AngelVeloz1506/TEAM-DELTA-WRO-2025-Panama/models/Prototypes/v2.jpg

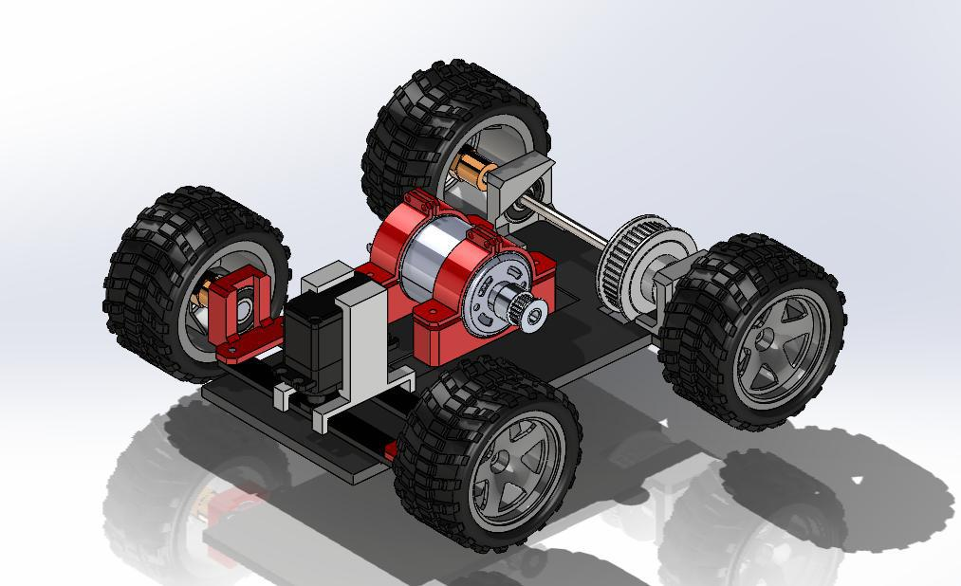
models/Prototypes/v2.jpg
