AngelVeloz1506/TEAM-DELTA-WRO-2025-Panama/models/Prototypes/v3.jpg

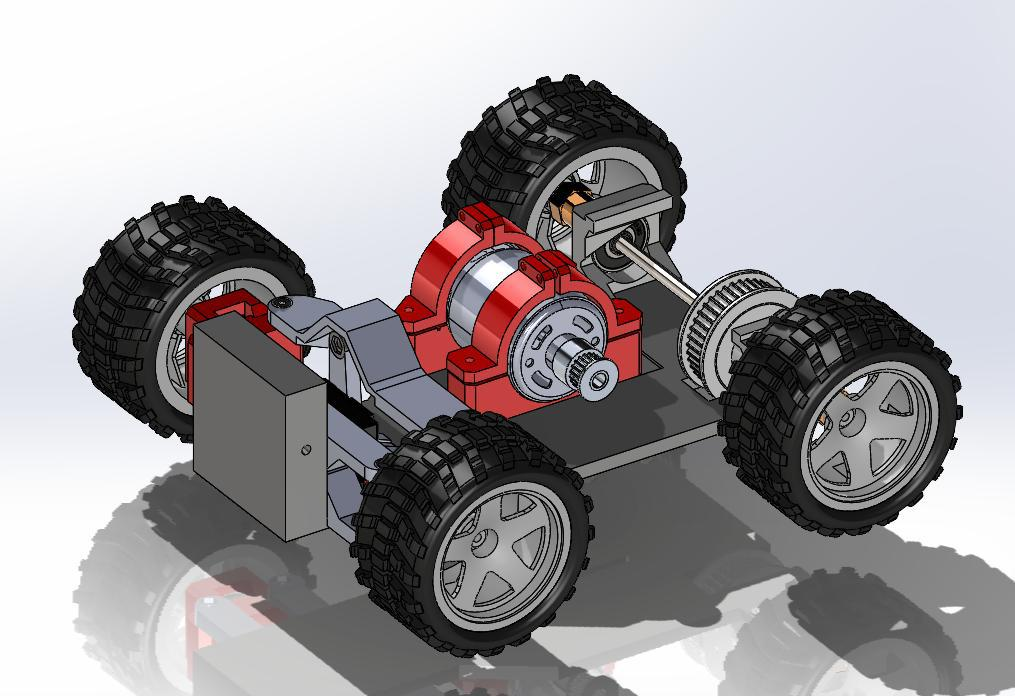
models/Prototypes/v3.jpg
