AngelVeloz1506/TEAM-DELTA-WRO-2025-Panama/v-photos/delta.jpg

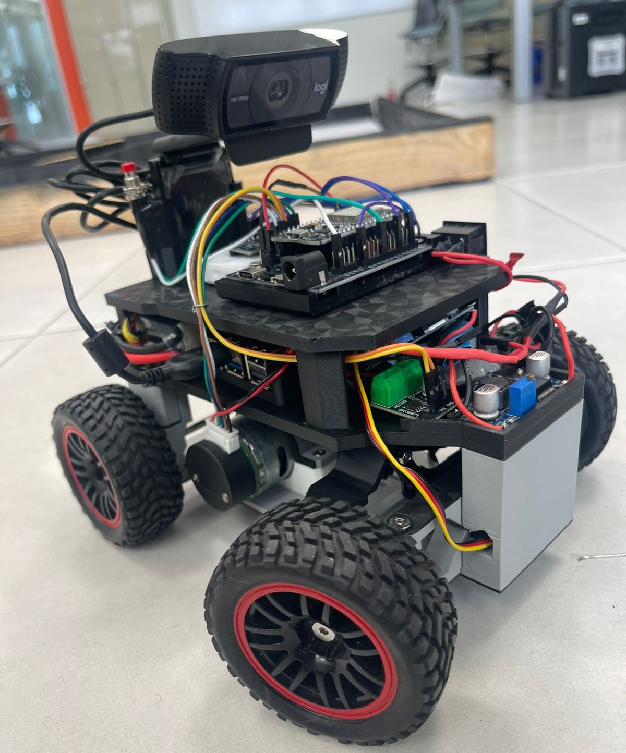
v-photos/delta.jpg
