AngelVeloz1506/TEAM-DELTA-WRO-2025-Panama/v-photos/first pic.jpg

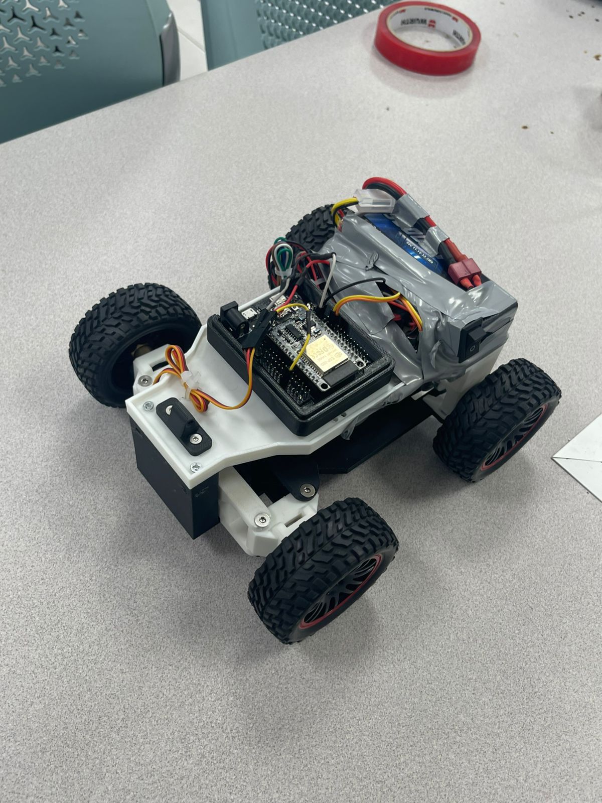
v-photos/first pic.jpg
