AngelVeloz1506/TEAM-DELTA-WRO-2025-Panama/models/Prototypes/V6.5/STL/Separador.SLDPRT

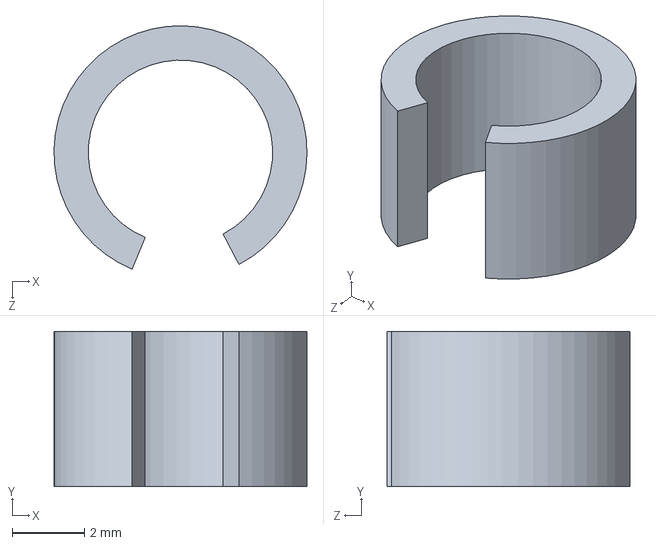
[picture p47: CAD file, 2025-08-24]
models/Prototypes/V6.5/STL/Separador.SLDPRT
7.00 x 4.30 x 6.73 mm
