AngelVeloz1506/TEAM-DELTA-WRO-2025-Panama/models/Prototypes/V6.5/Ultrasonic sensor.SLDPRT

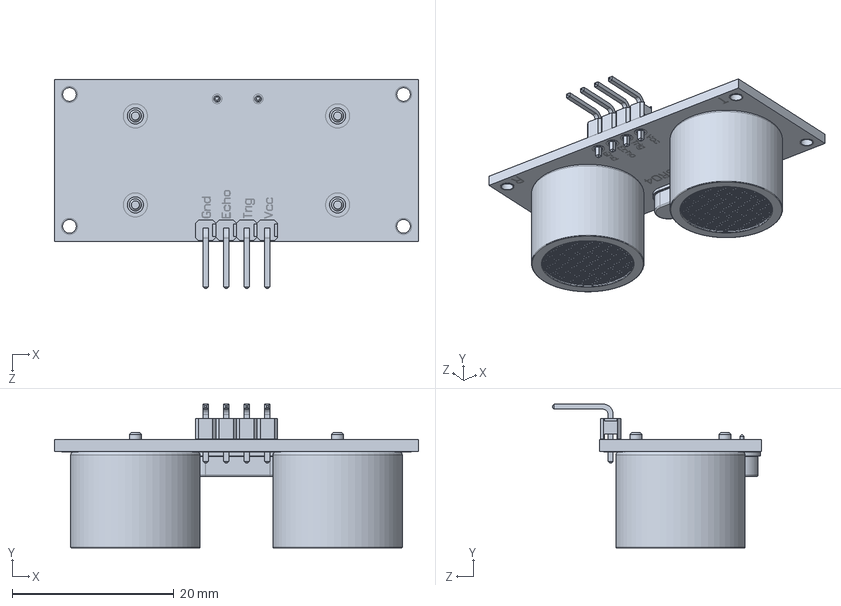
[picture p48: CAD file, 2025-10-17]
models/Prototypes/V6.5/Ultrasonic sensor.SLDPRT
45.0 x 17.8 x 25.8 mm
