AngelVeloz1506/TEAM-DELTA-WRO-2025-Panama/models/V7/Giro 2.SLDPRT

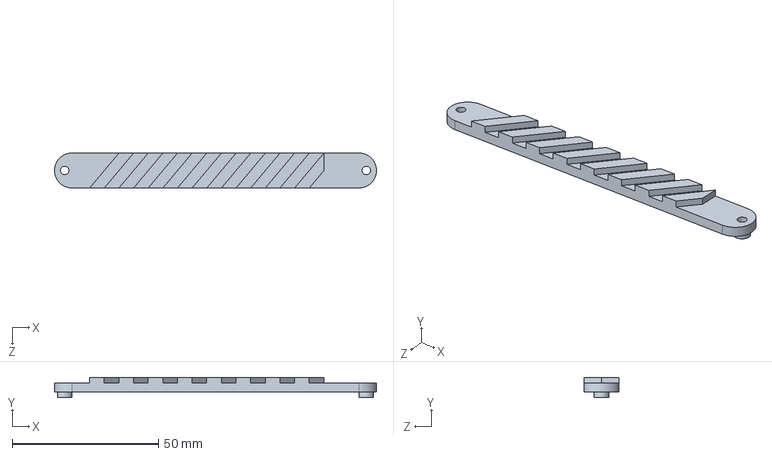
[picture p49: CAD file, 2025-10-18]
models/V7/Giro 2.SLDPRT
110.0 x 7.00 x 12.0 mm
