AngelVeloz1506/TEAM-DELTA-WRO-2025-Panama/models/V7/STL/rrep/V6.5 - Giro 2pr-1-1.STL

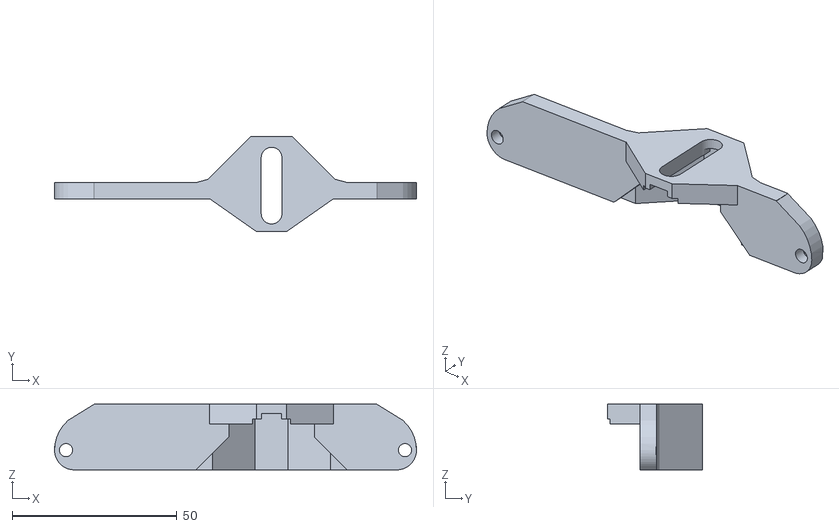
[picture p50: CAD file, 2025-10-18]
models/V7/STL/rrep/V6.5 - Giro 2pr-1-1.STL
110.0 x 29.0 x 20.0
