AngelVeloz1506/TEAM-DELTA-WRO-2025-Panama/models/V7/STL/V6.5 - Assem1-1 Ultr1 (2)-1.STL

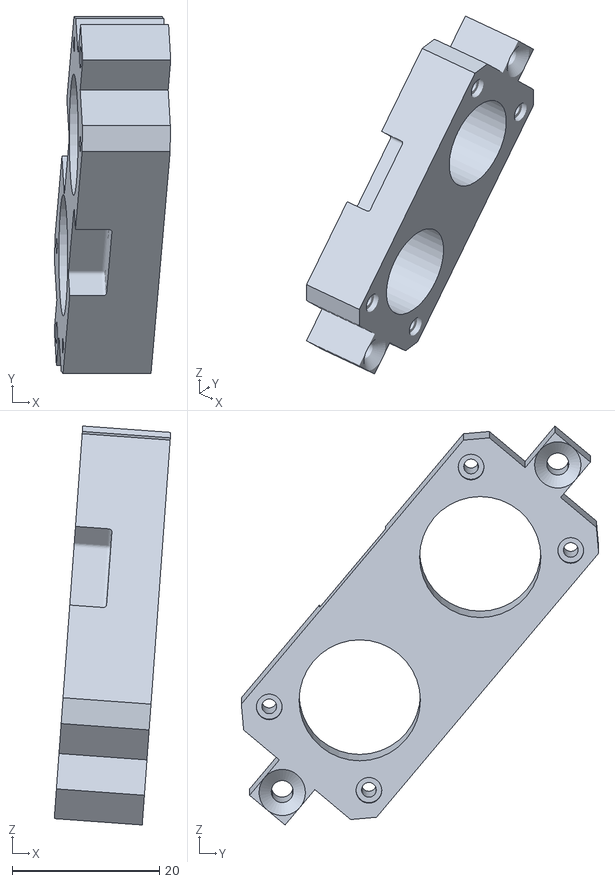
[picture p51: CAD file, 2025-10-18]
models/V7/STL/V6.5 - Assem1-1 Ultr1 (2)-1.STL
15.8 x 48.6 x 54.3
