AngelVeloz1506/TEAM-DELTA-WRO-2025-Panama/models/Prototypes/V6.5/Pulley2.step

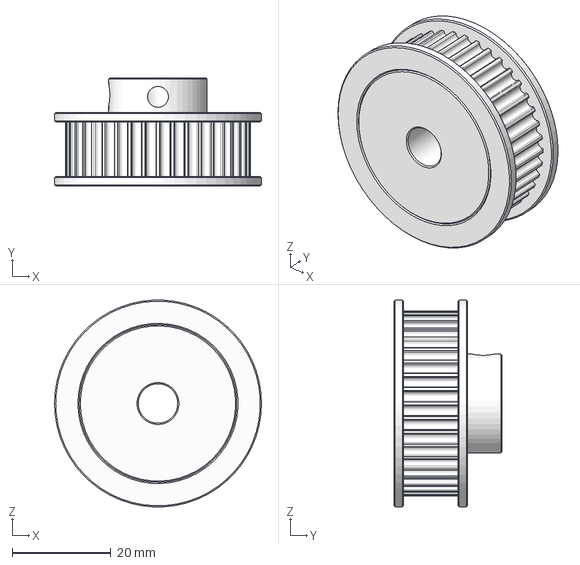
[picture p52: CAD file, 2025-08-24]
models/Prototypes/V6.5/Pulley2.step
42.0 x 22.0 x 41.9 mm
