AngelVeloz1506/TEAM-DELTA-WRO-2025-Panama/models/V7/STL/rrep/V6.5 - Pasador-1.STL

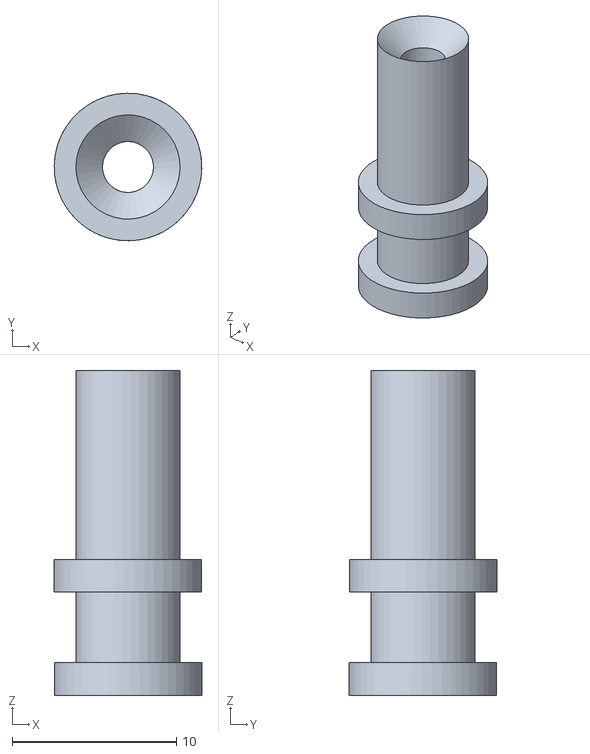
[picture p53: CAD file, 2025-10-18]
models/V7/STL/rrep/V6.5 - Pasador-1.STL
9.00 x 9.00 x 19.8
