AngelVeloz1506/TEAM-DELTA-WRO-2025-Panama/models/Prototypes/V6.5/Multistar_3000mAh_4S_Lipo_Battery.SLDPRT

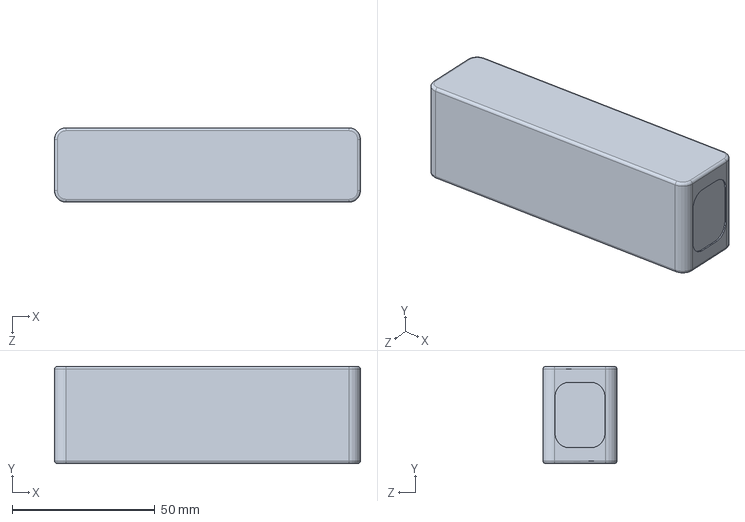
[picture p54: CAD file, 2025-08-24]
models/Prototypes/V6.5/Multistar_3000mAh_4S_Lipo_Battery.SLDPRT
107.0 x 34.0 x 26.0 mm
