AngelVeloz1506/TEAM-DELTA-WRO-2025-Panama/models/V7/Cam/Assem1 - CameraHolder2-1.STL

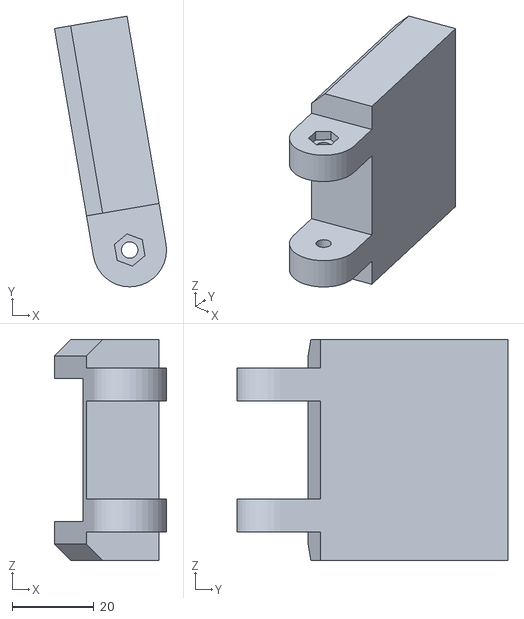
[picture p55: CAD file, 2025-10-18]
models/V7/Cam/Assem1 - CameraHolder2-1.STL
27.4 x 66.1 x 54.0
