AngelVeloz1506/TEAM-DELTA-WRO-2025-Panama/models/V7/STL/V6.5 - Assem1-1 Part2-1.STL

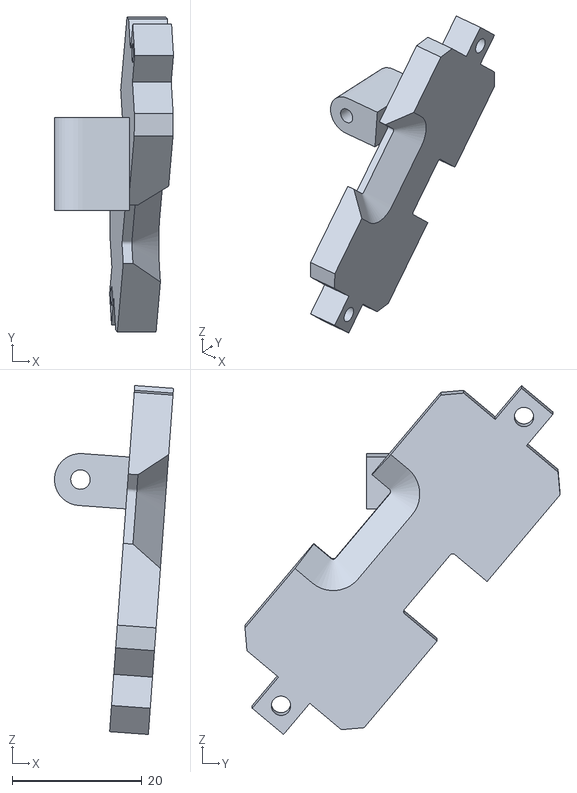
[picture p57: CAD file, 2025-10-18]
models/V7/STL/V6.5 - Assem1-1 Part2-1.STL
18.4 x 48.6 x 53.8
