AngelVeloz1506/TEAM-DELTA-WRO-2025-Panama/models/V7/Ultrasonico/Part2L.SLDPRT

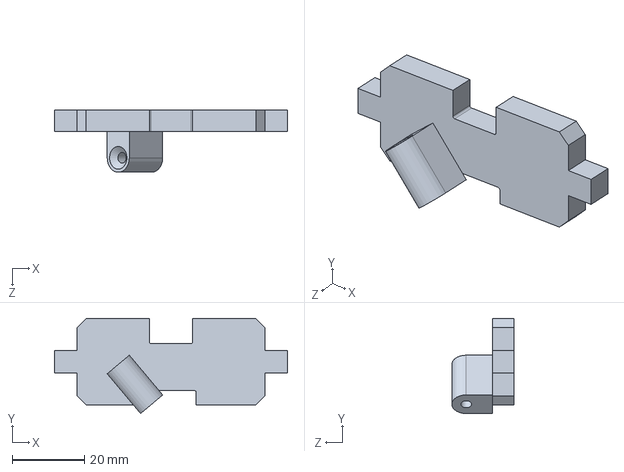
[picture p58: CAD file, 2025-10-18]
models/V7/Ultrasonico/Part2L.SLDPRT
64.6 x 26.4 x 17.3 mm
