AngelVeloz1506/TEAM-DELTA-WRO-2025-Panama/models/V7/V3.1Tyre.SLDPRT

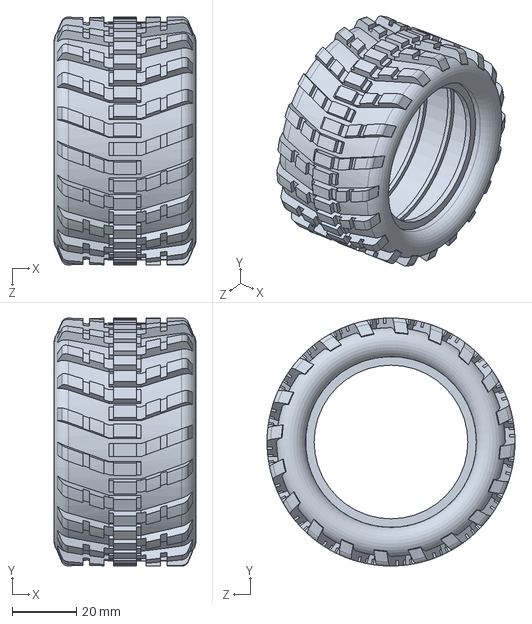
[picture p59: CAD file, 2025-10-18]
models/V7/V3.1Tyre.SLDPRT
43.9 x 77.0 x 77.0 mm
