AngelVeloz1506/TEAM-DELTA-WRO-2025-Panama/models/Prototypes/V6.5/001.SLDPRT

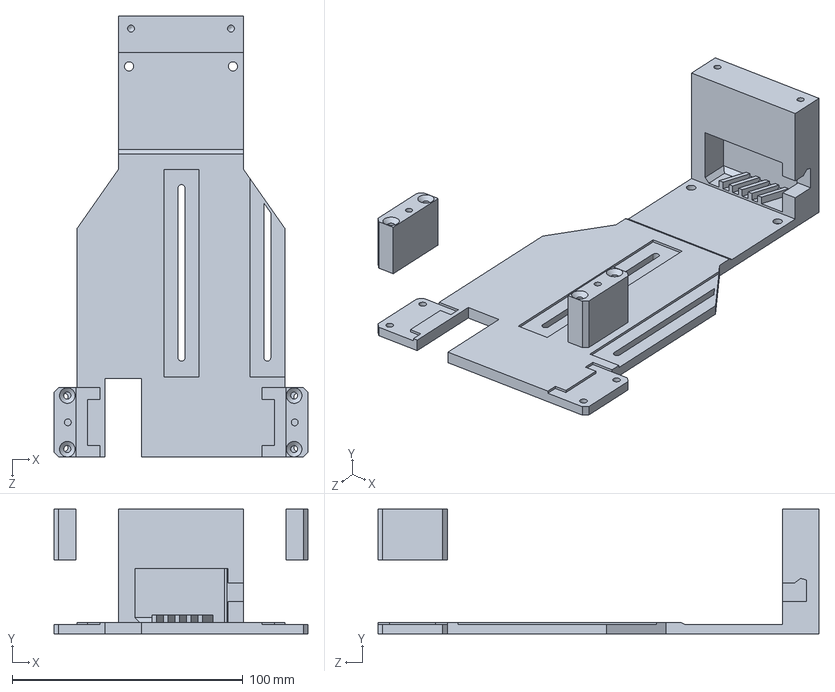
[picture p60: CAD file, 2025-08-24]
models/Prototypes/V6.5/001.SLDPRT
110.0 x 54.0 x 191.0 mm
