AngelVeloz1506/TEAM-DELTA-WRO-2025-Panama/models/V7/Cam/Assem1 - Part2-1.STL

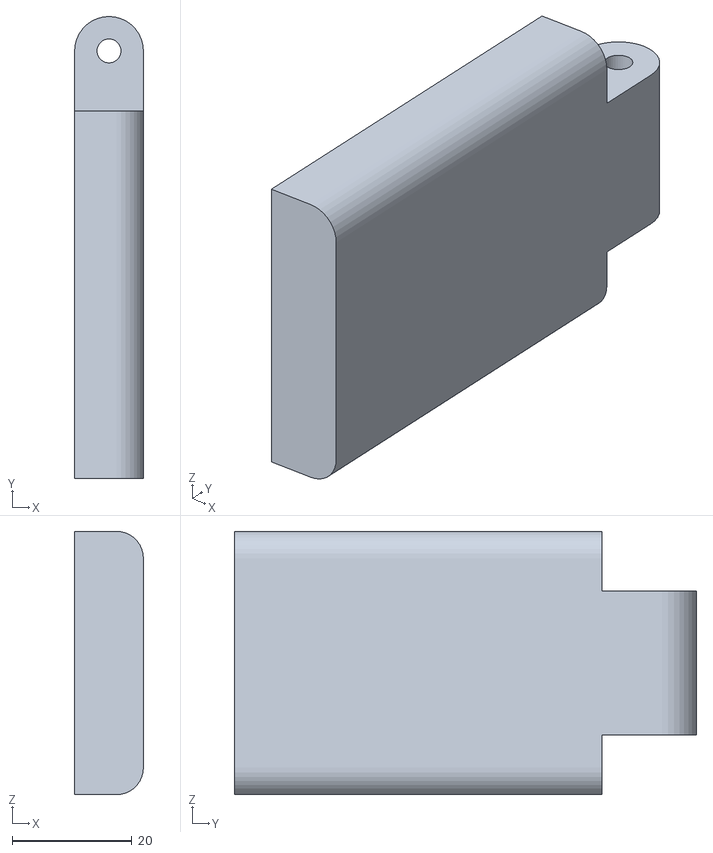
[picture p61: CAD file, 2025-10-18]
models/V7/Cam/Assem1 - Part2-1.STL
11.5 x 77.2 x 44.0
