AngelVeloz1506/TEAM-DELTA-WRO-2025-Panama/models/V7/STL/rrep/V6.5 - Ultr1 (2)-1-1.STL

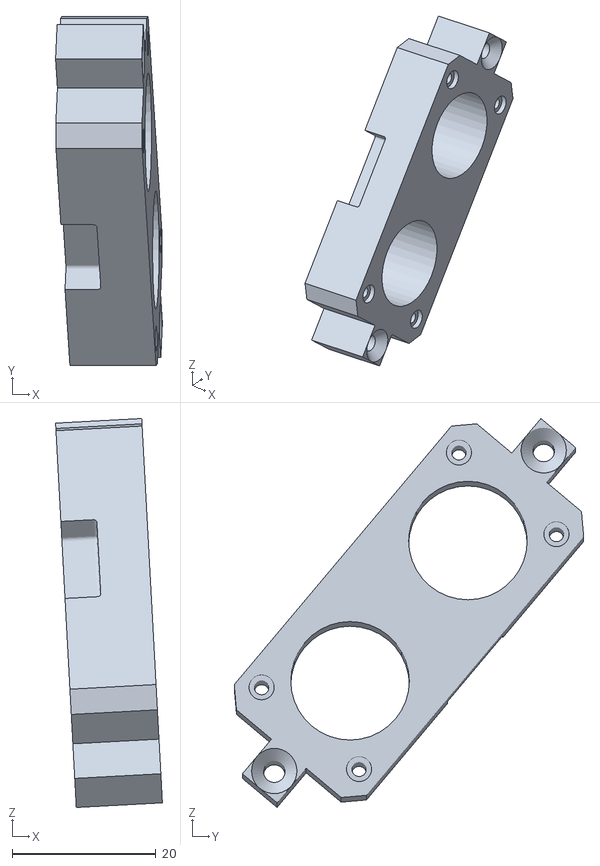
[picture p62: CAD file, 2025-10-18]
models/V7/STL/rrep/V6.5 - Ultr1 (2)-1-1.STL
14.9 x 48.6 x 54.1
