AngelVeloz1506/TEAM-DELTA-WRO-2025-Panama/models/V7/STL/SteeringCoupler.SLDPRT

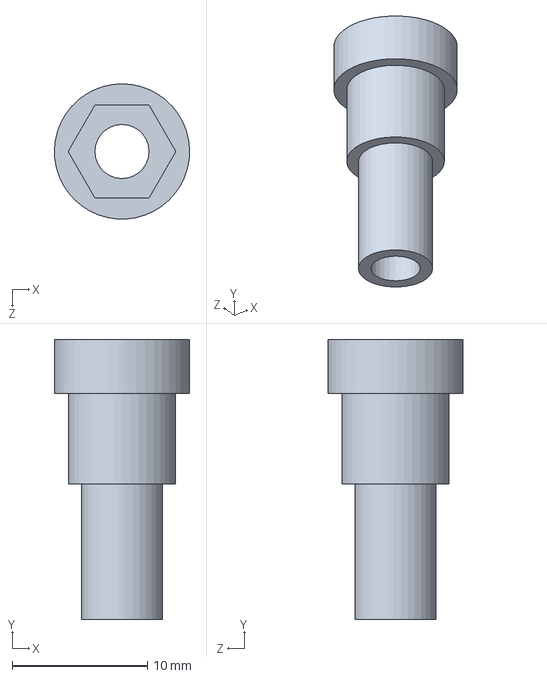
[picture p63: CAD file, 2025-10-18]
models/V7/STL/SteeringCoupler.SLDPRT
9.99 x 20.7 x 10.0 mm
