AngelVeloz1506/TEAM-DELTA-WRO-2025-Panama/models/V7/Ultrasonico/Ultr1 (2).SLDPRT

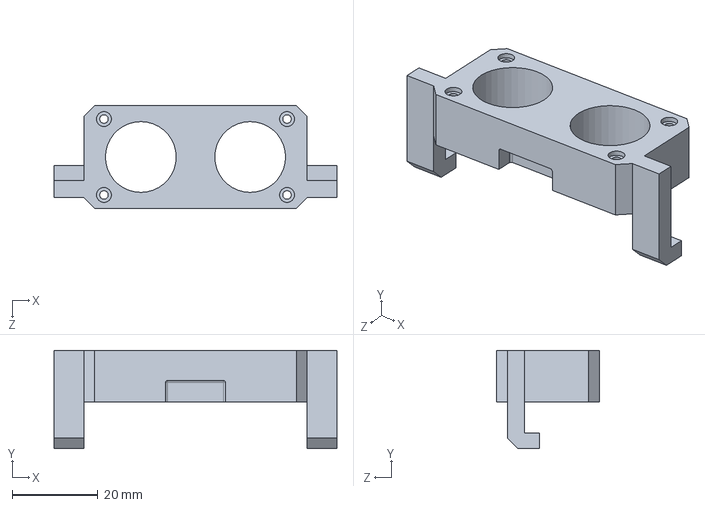
[picture p64: CAD file, 2025-10-18]
models/V7/Ultrasonico/Ultr1 (2).SLDPRT
66.0 x 22.9 x 24.0 mm
