AngelVeloz1506/TEAM-DELTA-WRO-2025-Panama/models/Prototypes/V6.5/MotorHolderL.SLDPRT

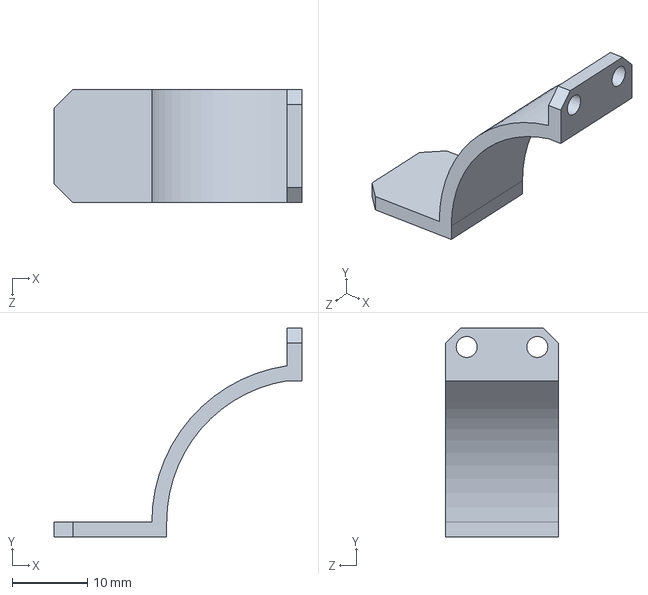
[picture p65: CAD file, 2025-08-24]
models/Prototypes/V6.5/MotorHolderL.SLDPRT
33.0 x 27.8 x 15.0 mm
