AngelVeloz1506/TEAM-DELTA-WRO-2025-Panama/models/V7/PixyCase1.1.SLDPRT

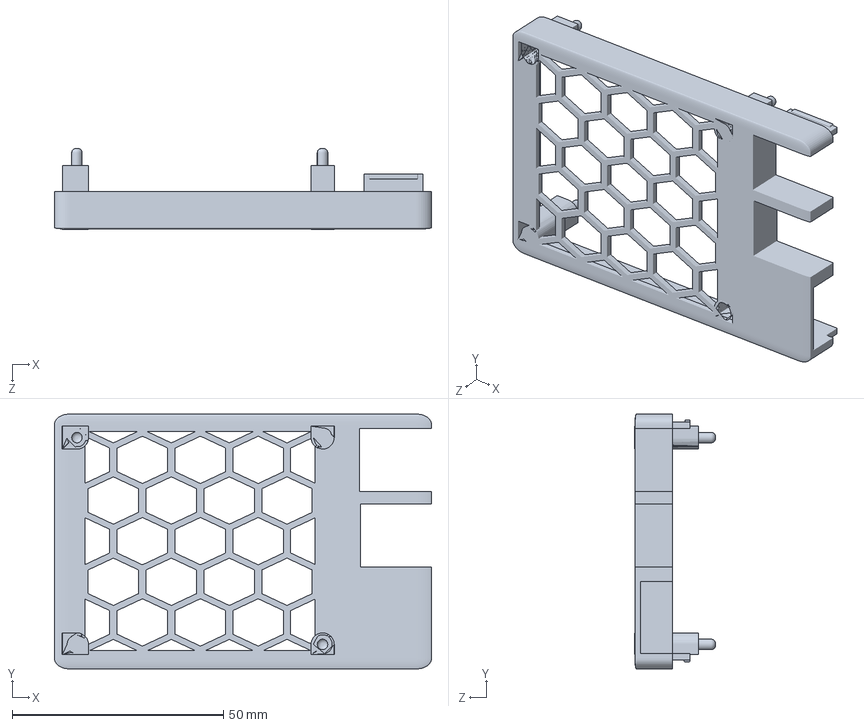
[picture p66: CAD file, 2025-10-18]
models/V7/PixyCase1.1.SLDPRT
89.3 x 60.4 x 19.2 mm
