AngelVeloz1506/TEAM-DELTA-WRO-2025-Panama/models/V7/STL/rrep/V6.5 - pulley11-1.STL

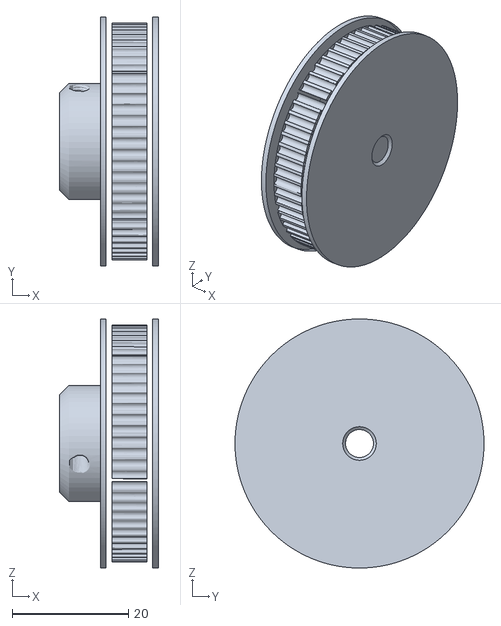
[picture p67: CAD file, 2025-10-18]
models/V7/STL/rrep/V6.5 - pulley11-1.STL
17.0 x 42.9 x 42.9
