AngelVeloz1506/TEAM-DELTA-WRO-2025-Panama/models/V7/001.SLDPRT

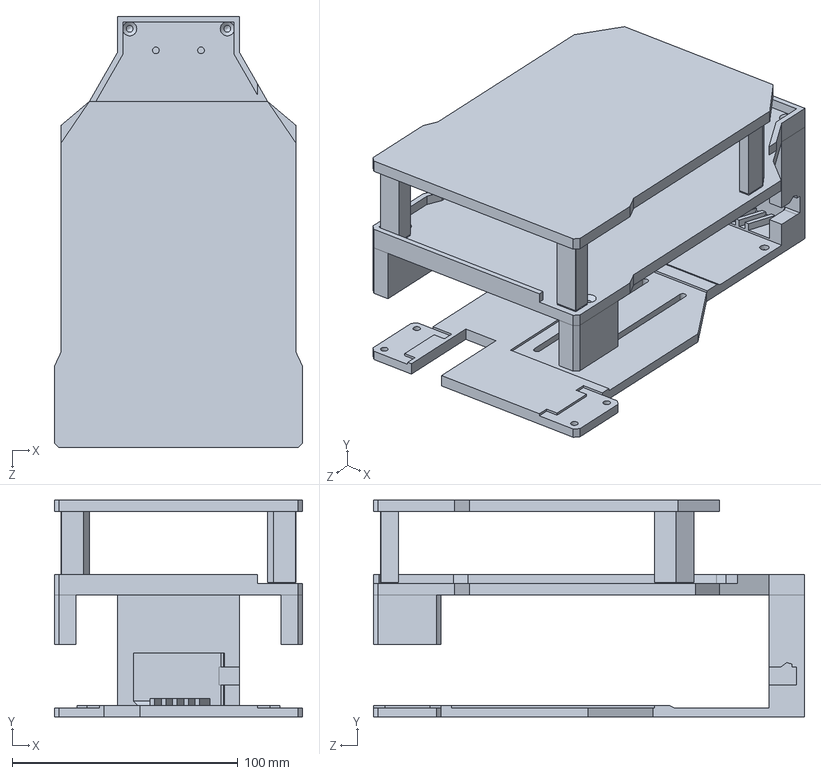
[picture p68: CAD file, 2025-10-18]
models/V7/001.SLDPRT
110.0 x 96.0 x 191.0 mm
