AngelVeloz1506/TEAM-DELTA-WRO-2025-Panama/models/Prototypes/V6.5/XT60 Buchse.SLDPRT

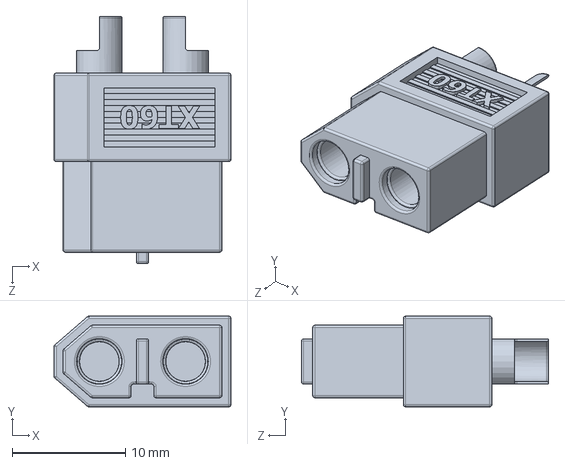
[picture p69: CAD file, 2025-08-24]
models/Prototypes/V6.5/XT60 Buchse.SLDPRT
15.6 x 8.00 x 21.8 mm
