AngelVeloz1506/TEAM-DELTA-WRO-2025-Panama/models/V7/Wheel2Bear.SLDPRT

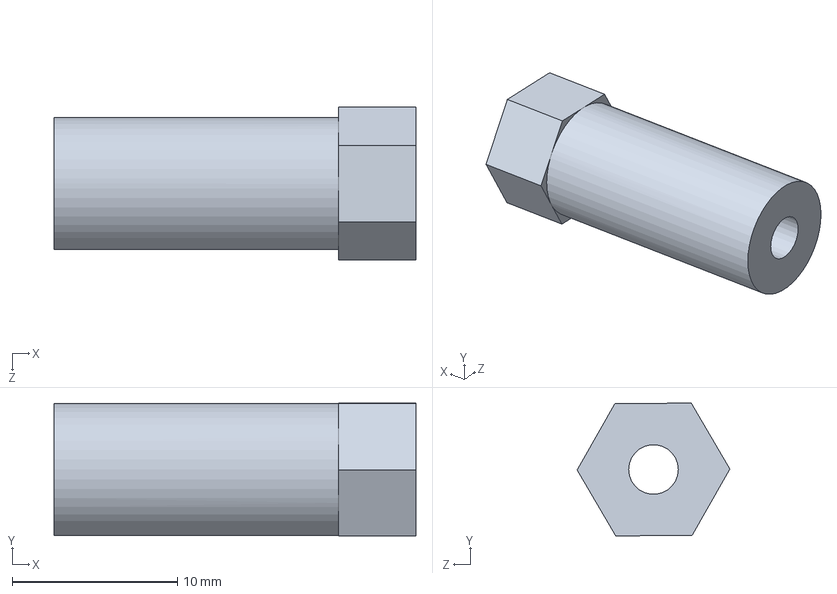
[picture p70: CAD file, 2025-10-18]
models/V7/Wheel2Bear.SLDPRT
21.9 x 8.03 x 9.24 mm
