AngelVeloz1506/TEAM-DELTA-WRO-2025-Panama/models/Prototypes/V6.5/MotorHolder2.5B.SLDPRT

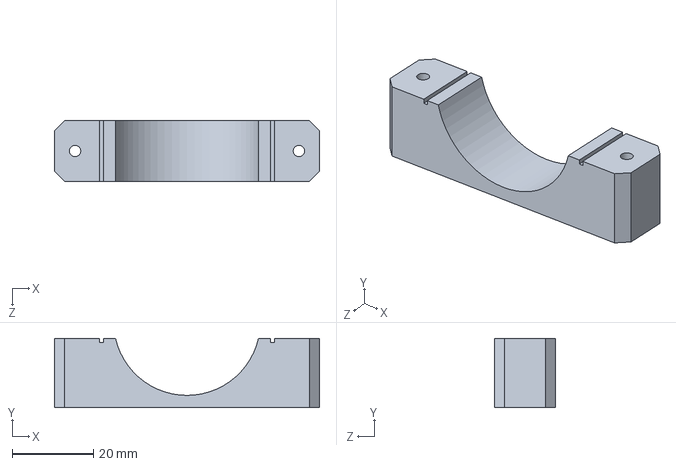
[picture p71: CAD file, 2025-08-24]
models/Prototypes/V6.5/MotorHolder2.5B.SLDPRT
65.1 x 17.0 x 15.0 mm
