AngelVeloz1506/TEAM-DELTA-WRO-2025-Panama/models/V7/Giro 2.1.SLDPRT

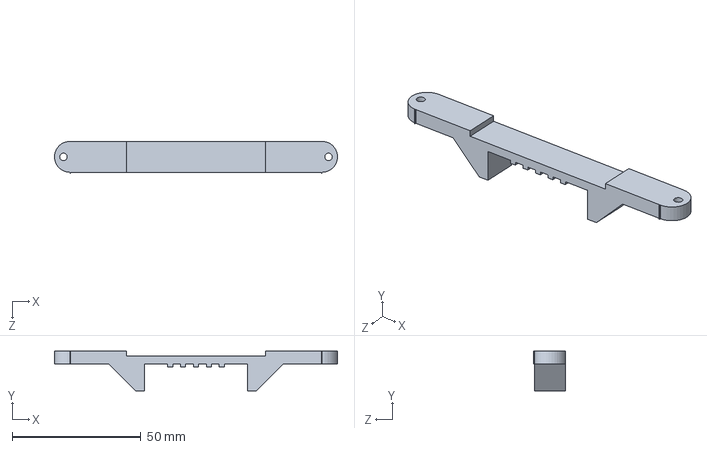
[picture p72: CAD file, 2025-10-18]
models/V7/Giro 2.1.SLDPRT
109.9 x 15.5 x 12.5 mm
