AngelVeloz1506/TEAM-DELTA-WRO-2025-Panama/models/V7/STL/rrep/V6.5 - Part2-1.STL

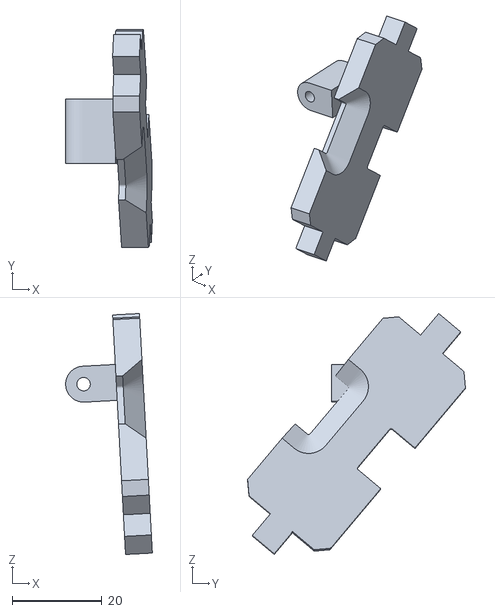
[picture p73: CAD file, 2025-10-18]
models/V7/STL/rrep/V6.5 - Part2-1.STL
19.4 x 48.6 x 53.8
