AngelVeloz1506/TEAM-DELTA-WRO-2025-Panama/models/Prototypes/V6.5/Pulley1.SLDPRT

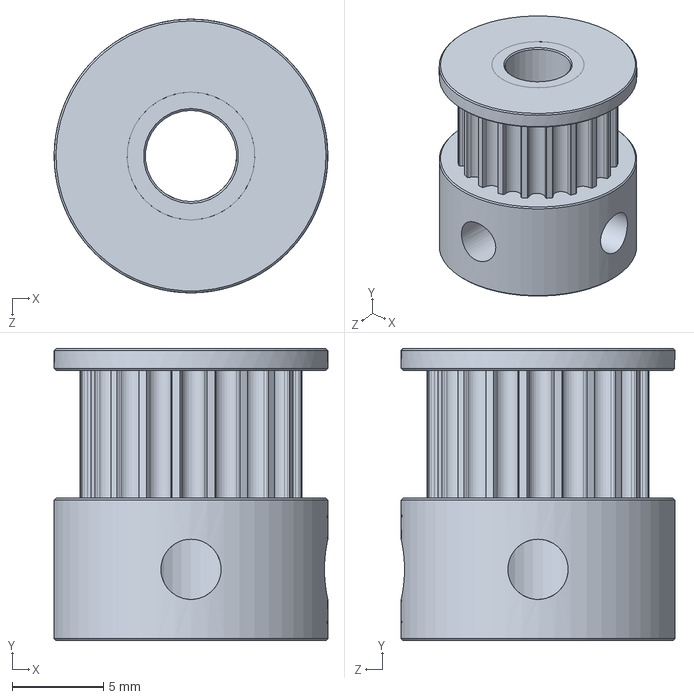
[picture p74: CAD file, 2025-08-24]
models/Prototypes/V6.5/Pulley1.SLDPRT
15.0 x 16.0 x 15.0 mm
