AngelVeloz1506/TEAM-DELTA-WRO-2025-Panama/models/Prototypes/V6.5/Shaft2HexCoupling.SLDPRT

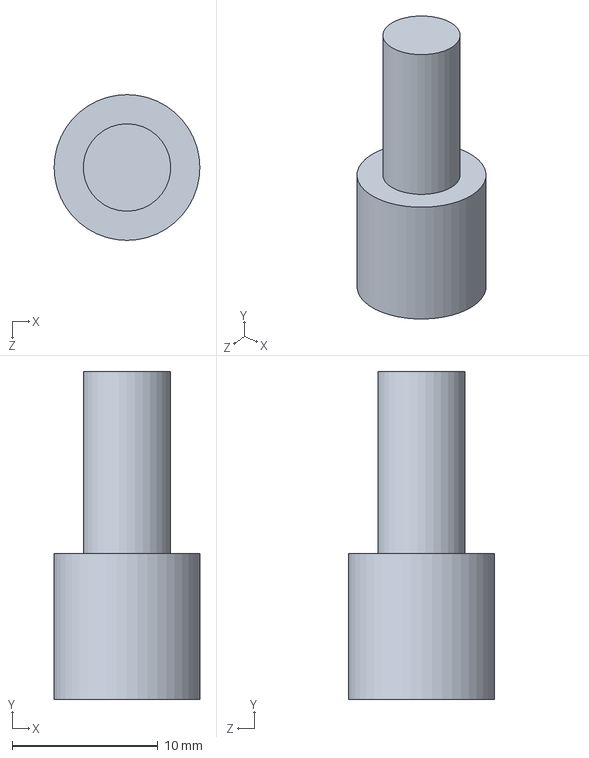
[picture p76: CAD file, 2025-08-24]
models/Prototypes/V6.5/Shaft2HexCoupling.SLDPRT
10.0 x 22.5 x 10.0 mm
