AngelVeloz1506/TEAM-DELTA-WRO-2025-Panama/models/V7/RowlockB.SLDPRT

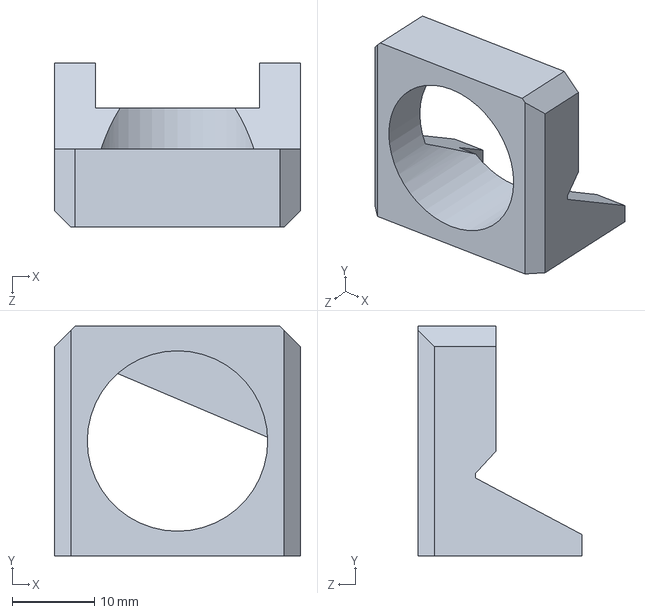
[picture p77: CAD file, 2025-10-18]
models/V7/RowlockB.SLDPRT
30.0 x 28.0 x 20.0 mm
