AngelVeloz1506/TEAM-DELTA-WRO-2025-Panama/models/V7/STL/rrep/V6.5 - Giro 2.1-1-1.STL

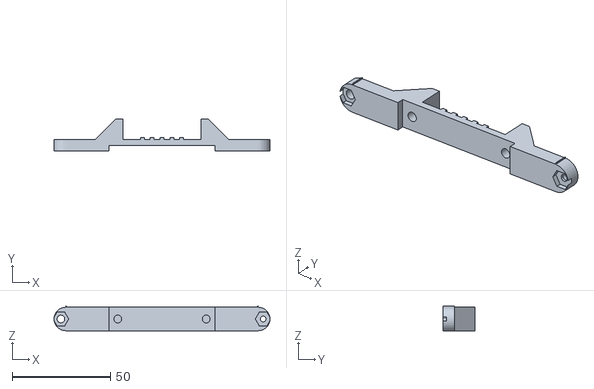
[picture p78: CAD file, 2025-10-18]
models/V7/STL/rrep/V6.5 - Giro 2.1-1-1.STL
110.0 x 16.5 x 12.5
