AngelVeloz1506/TEAM-DELTA-WRO-2025-Panama/models/Prototypes/V6.5/DC Motor 555_12V.SLDPRT

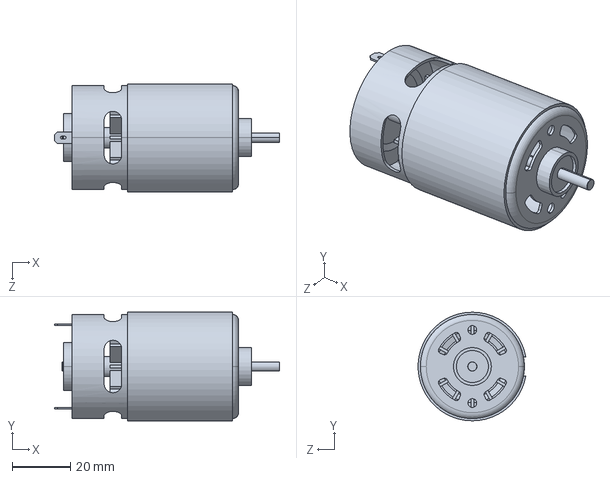
[picture p81: CAD file, 2025-08-24]
models/Prototypes/V6.5/DC Motor 555_12V.SLDPRT
77.0 x 37.2 x 36.9 mm
