AngelVeloz1506/TEAM-DELTA-WRO-2025-Panama/models/V7/PixyCase2.2.SLDPRT

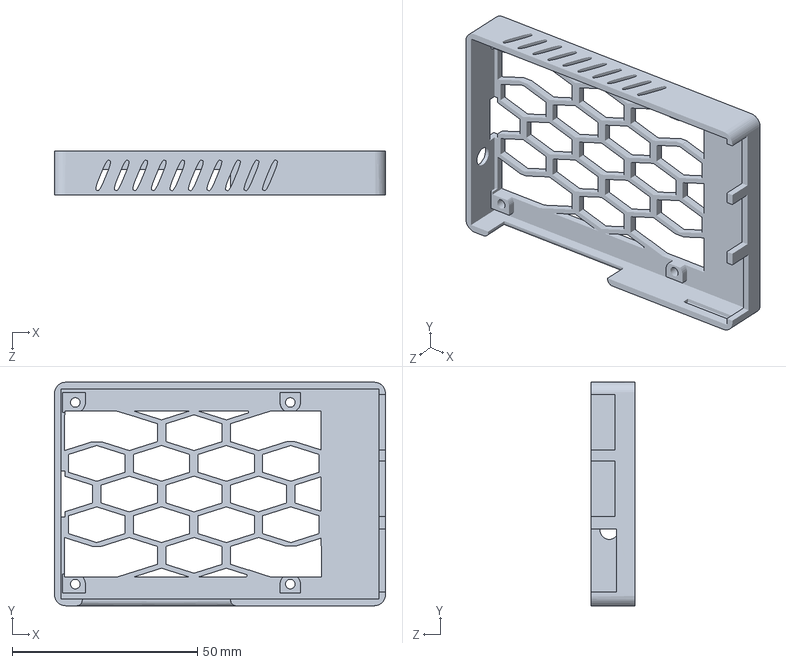
[picture p84: CAD file, 2025-10-18]
models/V7/PixyCase2.2.SLDPRT
89.3 x 60.3 x 12.0 mm
