AngelVeloz1506/TEAM-DELTA-WRO-2025-Panama/models/Prototypes/V6.5/Shaft.SLDPRT

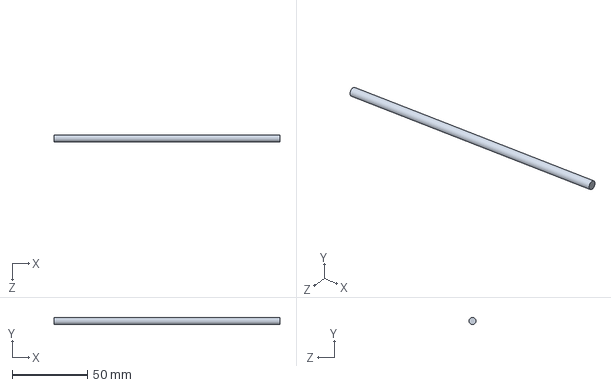
[picture p85: CAD file, 2025-08-24]
models/Prototypes/V6.5/Shaft.SLDPRT
150.0 x 4.69 x 4.70 mm
