AngelVeloz1506/TEAM-DELTA-WRO-2025-Panama/models/V7/Giro 4.SLDPRT

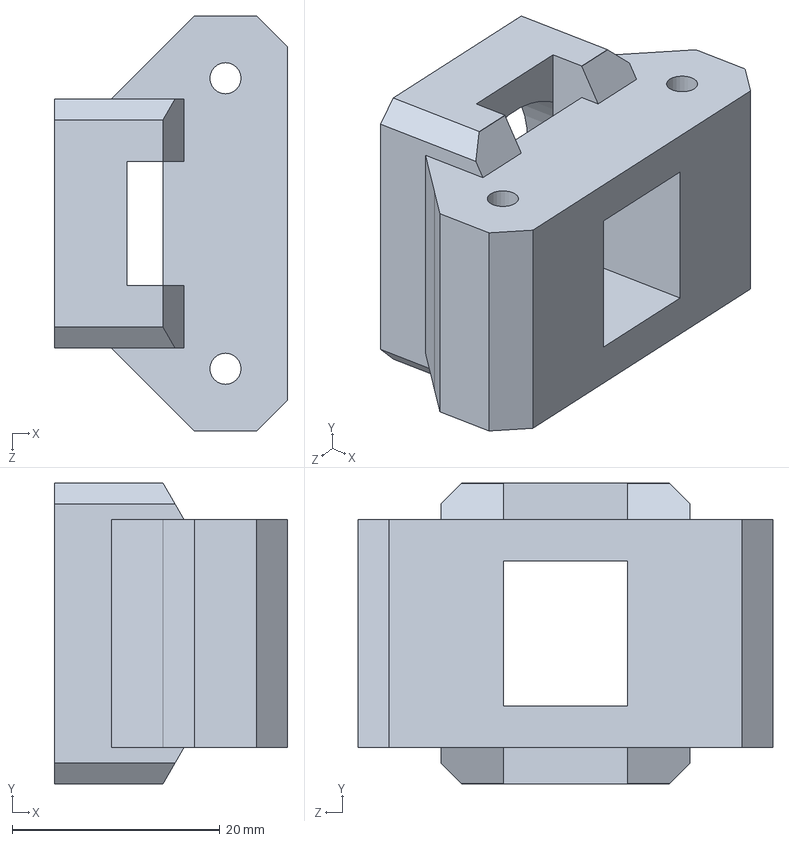
[picture p86: CAD file, 2025-10-18]
models/V7/Giro 4.SLDPRT
22.5 x 29.0 x 40.0 mm
