AngelVeloz1506/TEAM-DELTA-WRO-2025-Panama/models/V7/STL/rrep/V6.5 - RowlockB-1.STL

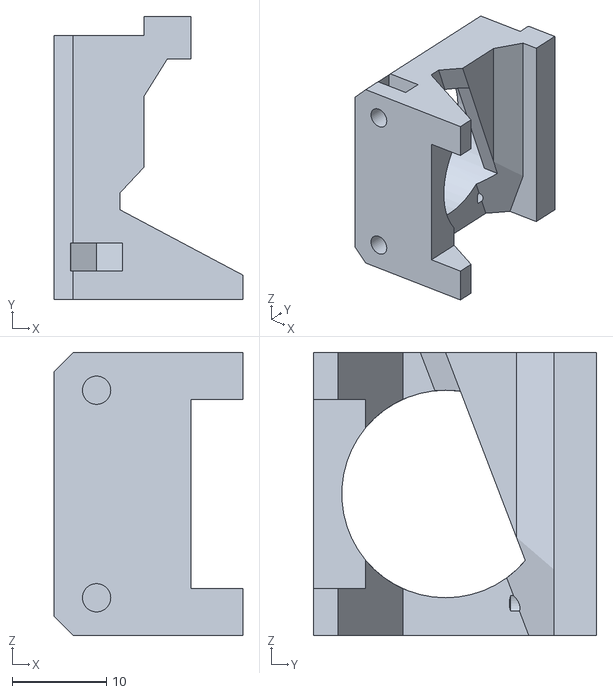
[picture p87: CAD file, 2025-10-18]
models/V7/STL/rrep/V6.5 - RowlockB-1.STL
20.0 x 30.0 x 30.0
