AngelVeloz1506/TEAM-DELTA-WRO-2025-Panama/models/Prototypes/V6.5/SteeringCoupler.SLDPRT

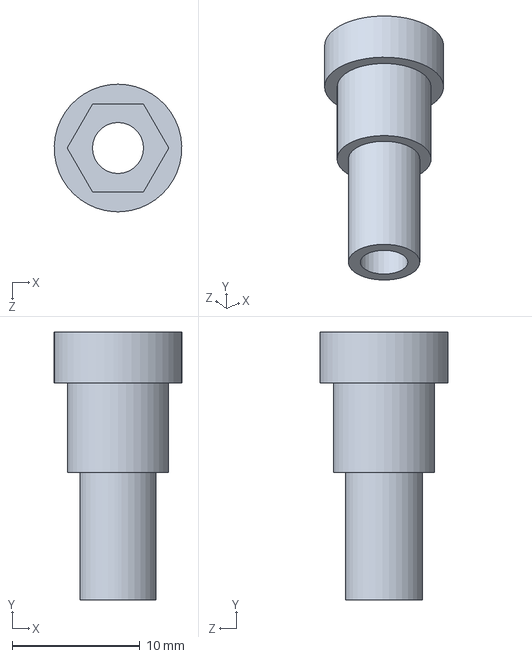
[picture p88: CAD file, 2025-08-24]
models/Prototypes/V6.5/SteeringCoupler.SLDPRT
9.99 x 21.0 x 10.0 mm
