AngelVeloz1506/TEAM-DELTA-WRO-2025-Panama/models/V7/V3.1Wheel.SLDPRT

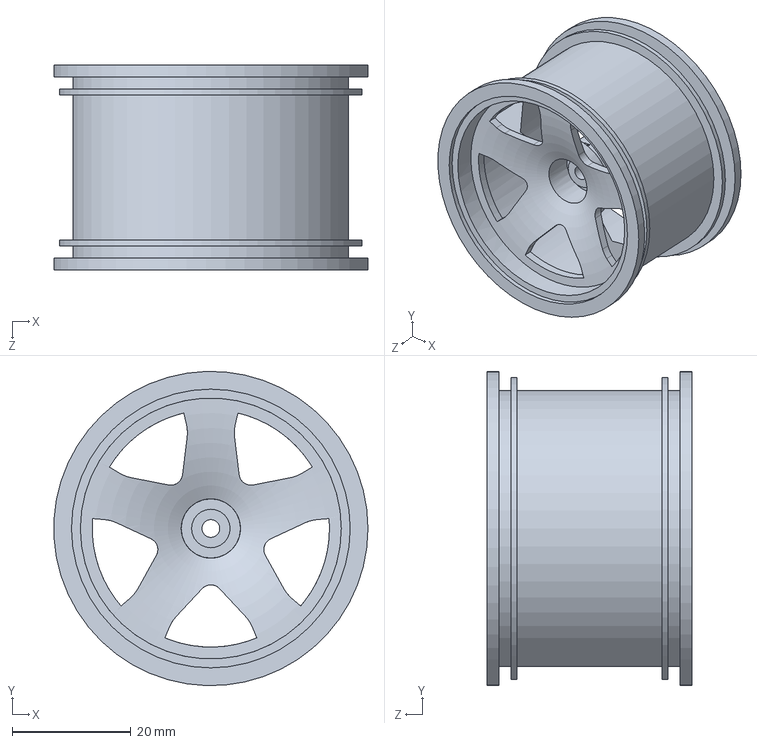
[picture p89: CAD file, 2025-08-24]
models/V7/V3.1Wheel.SLDPRT
52.9 x 53.0 x 34.5 mm
