AngelVeloz1506/TEAM-DELTA-WRO-2025-Panama/models/Prototypes/V6.5/PixyCase3.SLDPRT

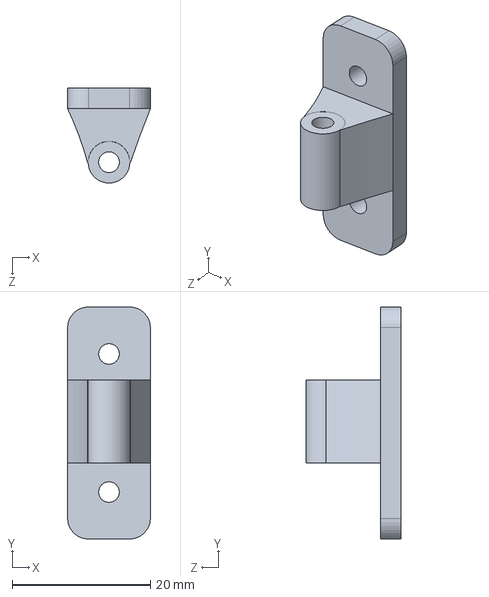
[picture p90: CAD file, 2025-08-24]
models/Prototypes/V6.5/PixyCase3.SLDPRT
12.0 x 33.6 x 13.8 mm
