AngelVeloz1506/TEAM-DELTA-WRO-2025-Panama/models/Prototypes/V6.5/Giro 4.SLDPRT

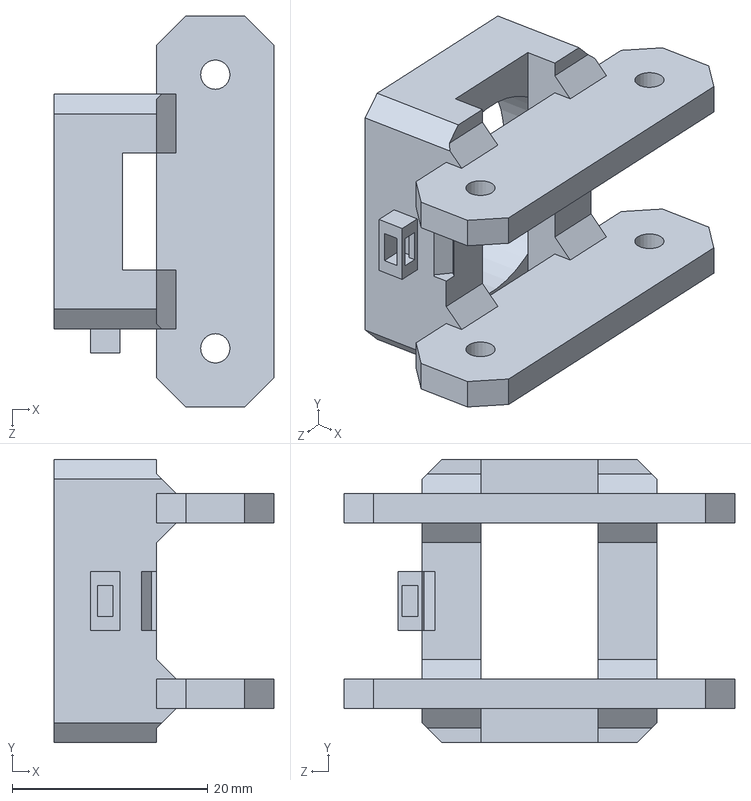
[picture p91: CAD file, 2025-08-24]
models/Prototypes/V6.5/Giro 4.SLDPRT
22.5 x 29.0 x 40.0 mm
