AngelVeloz1506/TEAM-DELTA-WRO-2025-Panama/models/V7/PixyCase1.SLDPRT

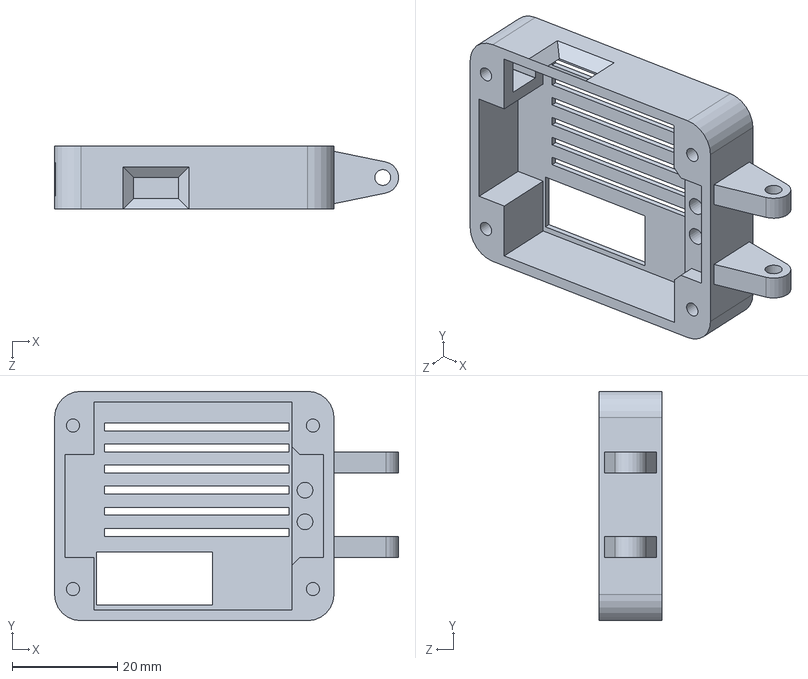
[picture p92: CAD file, 2025-08-24]
models/V7/PixyCase1.SLDPRT
65.2 x 43.5 x 12.0 mm
