AngelVeloz1506/TEAM-DELTA-WRO-2025-Panama/models/Prototypes/V6.5/MotorHolder2B.SLDPRT

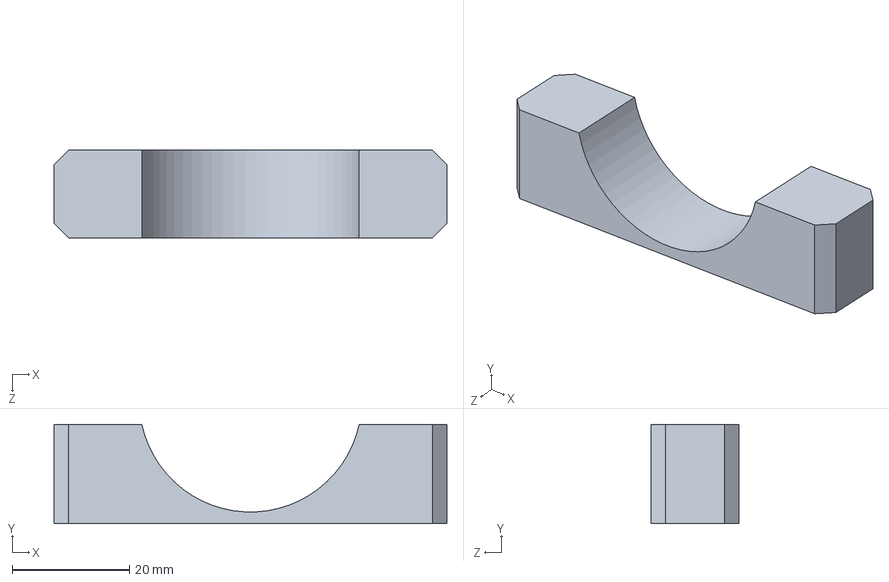
[picture p93: CAD file, 2025-08-24]
models/Prototypes/V6.5/MotorHolder2B.SLDPRT
67.1 x 17.0 x 15.0 mm
