AngelVeloz1506/TEAM-DELTA-WRO-2025-Panama/models/V7/Hex Coupling 6mm.SLDPRT

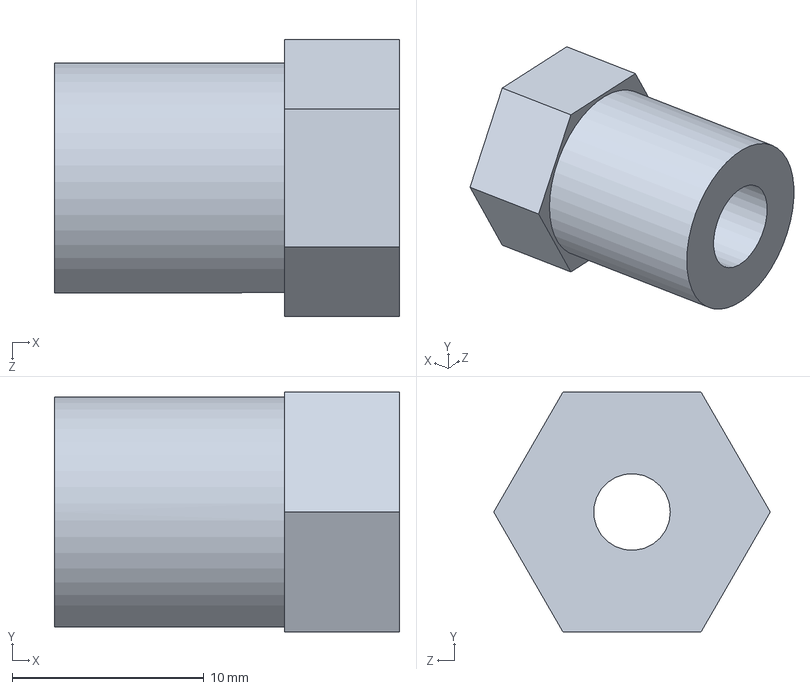
[picture p94: CAD file, 2025-08-24]
models/V7/Hex Coupling 6mm.SLDPRT
18.0 x 12.5 x 14.4 mm
