AngelVeloz1506/TEAM-DELTA-WRO-2025-Panama/models/Prototypes/V6.5/PixyCase2.SLDPRT

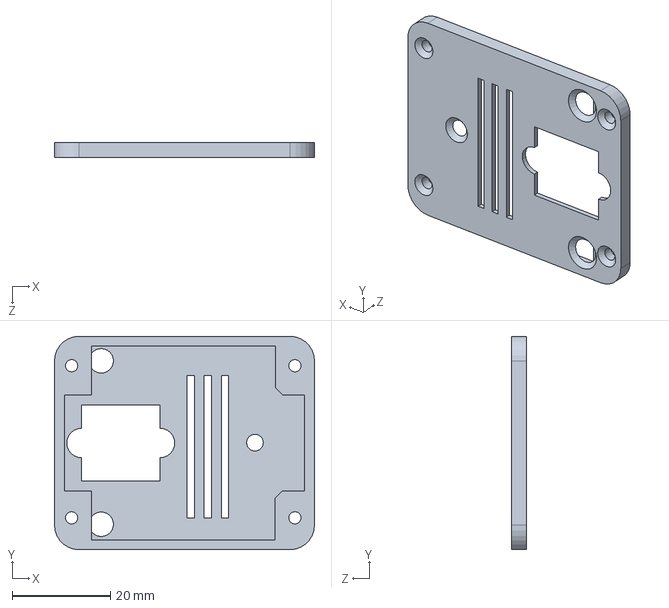
[picture p95: CAD file, 2025-08-24]
models/Prototypes/V6.5/PixyCase2.SLDPRT
53.0 x 43.5 x 3.00 mm
