AngelVeloz1506/TEAM-DELTA-WRO-2025-Panama/models/Prototypes/V6.5/ServoArm.SLDPRT

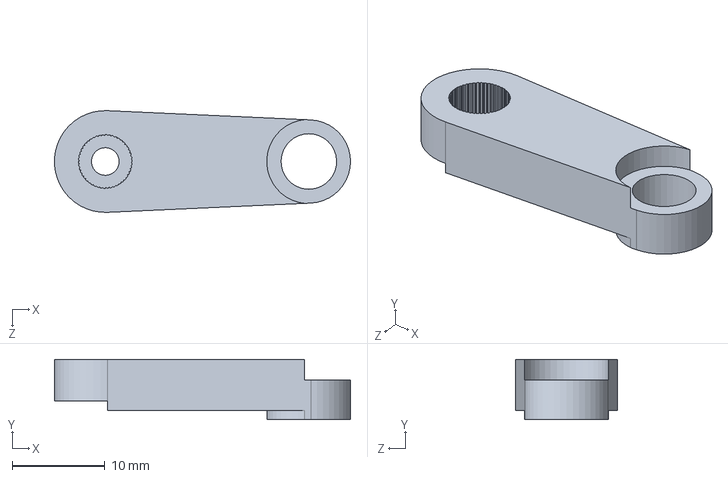
[picture p96: CAD file, 2025-08-24]
models/Prototypes/V6.5/ServoArm.SLDPRT
32.0 x 6.50 x 11.0 mm
