AngelVeloz1506/TEAM-DELTA-WRO-2025-Panama/models/V7/Bearing2Shaft.SLDPRT

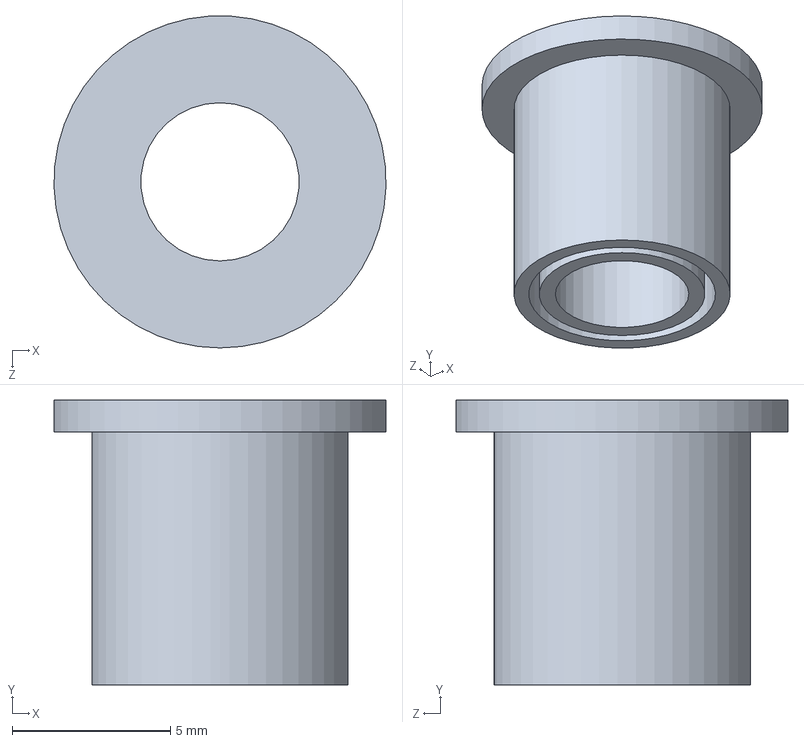
[picture p97: CAD file, 2025-08-24]
models/V7/Bearing2Shaft.SLDPRT
10.5 x 9.00 x 10.5 mm
