AngelVeloz1506/TEAM-DELTA-WRO-2025-Panama/models/Prototypes/V6.5/imu holderFront.SLDPRT

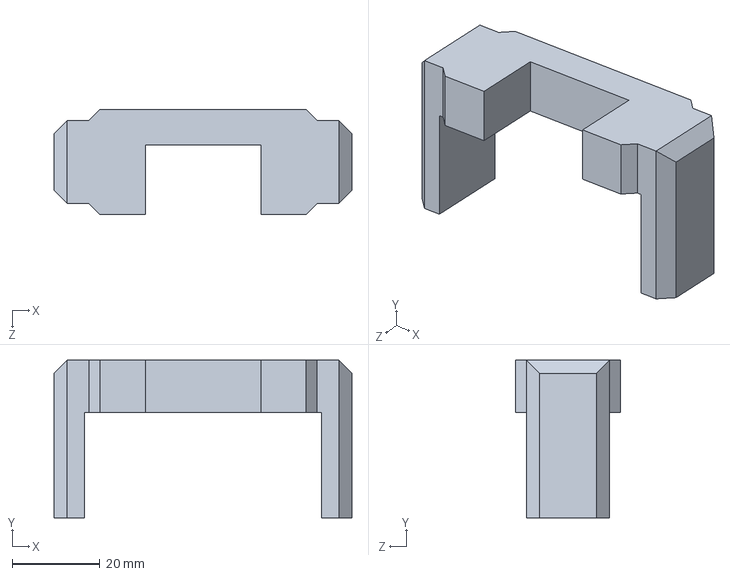
[picture p98: CAD file, 2025-08-24]
models/Prototypes/V6.5/imu holderFront.SLDPRT
68.0 x 36.0 x 24.0 mm
