AngelVeloz1506/TEAM-DELTA-WRO-2025-Panama/models/Prototypes/V6.5/WRO plugNplay.SLDPRT

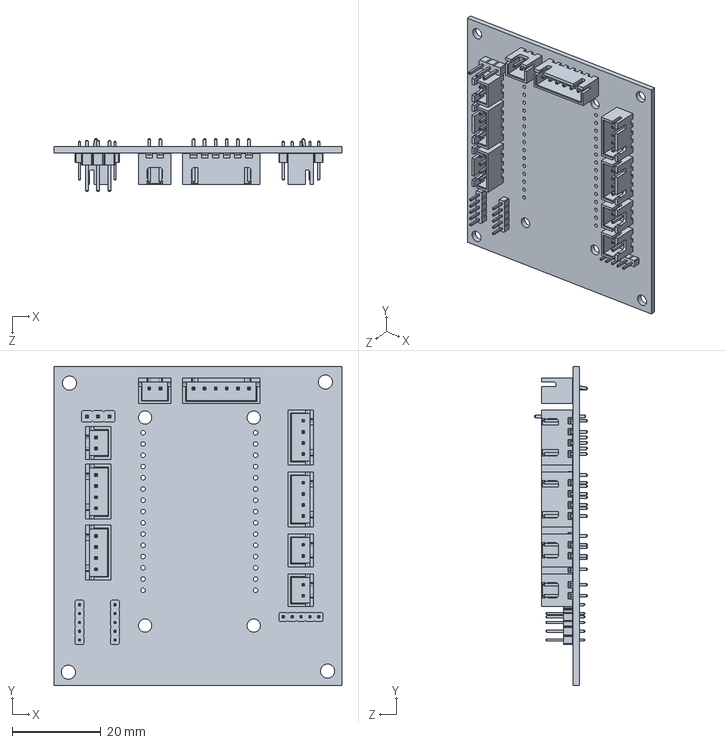
[picture p99: CAD file, 2025-08-24]
models/Prototypes/V6.5/WRO plugNplay.SLDPRT
65.0 x 72.0 x 11.9 mm
