AngelVeloz1506/TEAM-DELTA-WRO-2025-Panama/models/Prototypes/V6.5/ultrasonic holderFront.SLDPRT

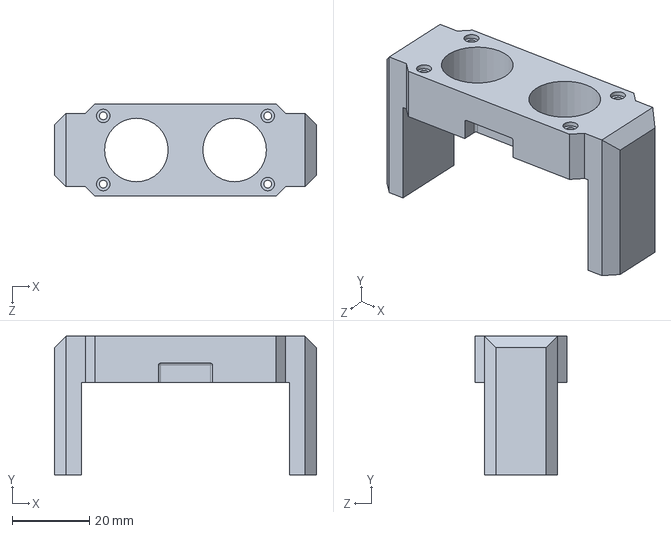
[picture p100: CAD file, 2025-08-24]
models/Prototypes/V6.5/ultrasonic holderFront.SLDPRT
68.0 x 36.0 x 24.0 mm
