AngelVeloz1506/TEAM-DELTA-WRO-2025-Panama/models/Prototypes/V6.5/mg995.SLDPRT

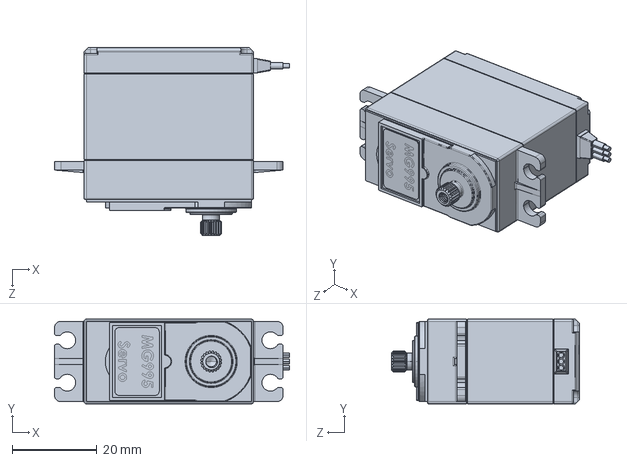
[picture p101: CAD file, 2025-08-24]
models/Prototypes/V6.5/mg995.SLDPRT
55.5 x 20.0 x 44.5 mm
