AngelVeloz1506/TEAM-DELTA-WRO-2025-Panama/models/V7/608RS.SLDPRT

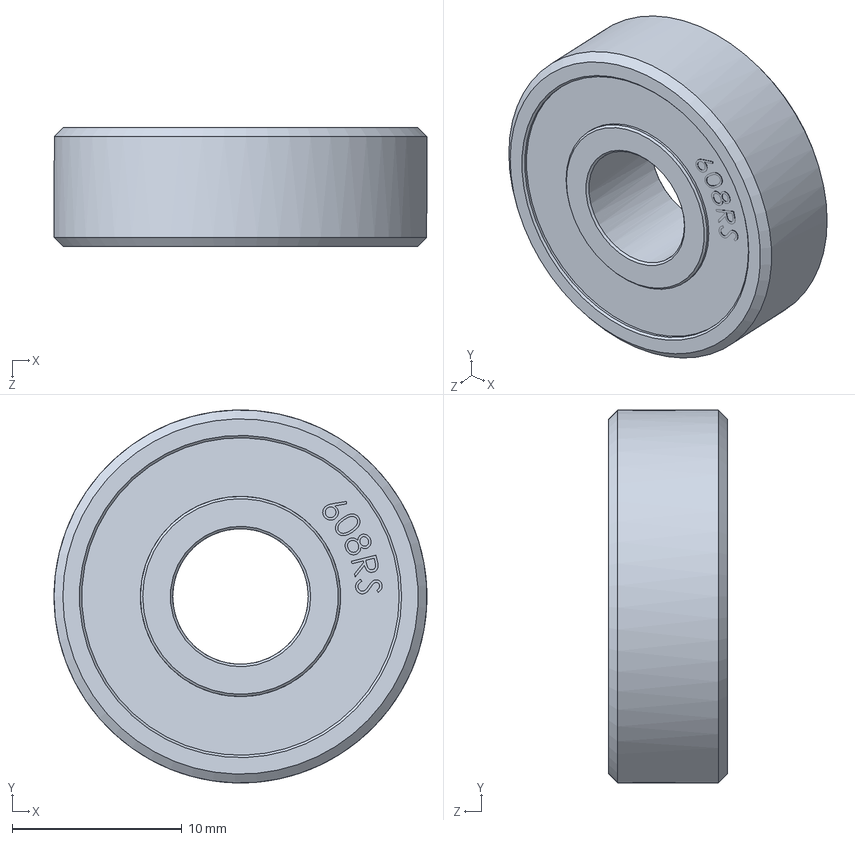
[picture p102: CAD file, 2025-08-24]
models/V7/608RS.SLDPRT
22.0 x 22.0 x 7.00 mm
