AngelVeloz1506/TEAM-DELTA-WRO-2025-Panama/models/Prototypes/V6.5/TopeServo.SLDPRT

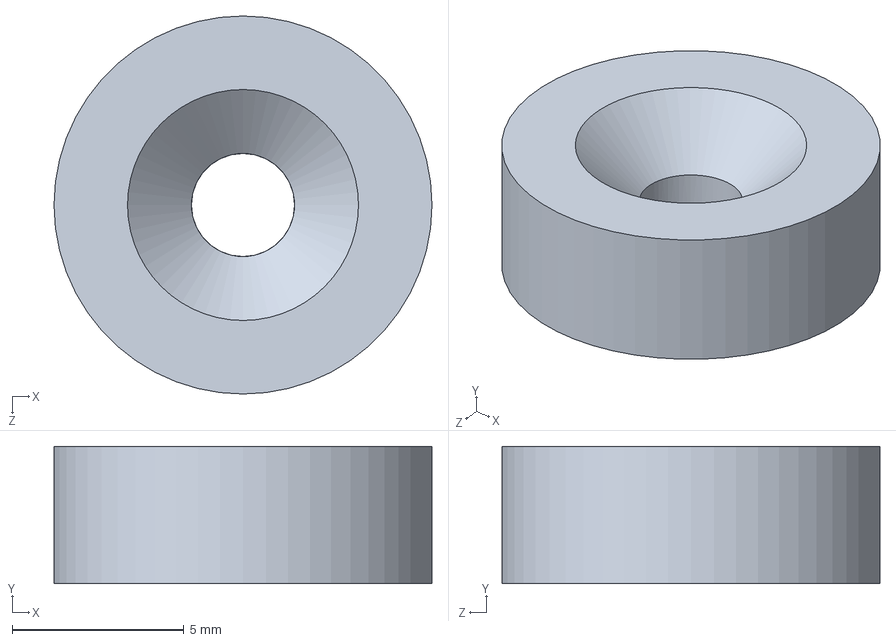
[picture p103: CAD file, 2025-08-24]
models/Prototypes/V6.5/TopeServo.SLDPRT
11.0 x 4.00 x 11.0 mm
