AngelVeloz1506/TEAM-DELTA-WRO-2025-Panama/models/Prototypes/V6.5/IMU case.SLDPRT

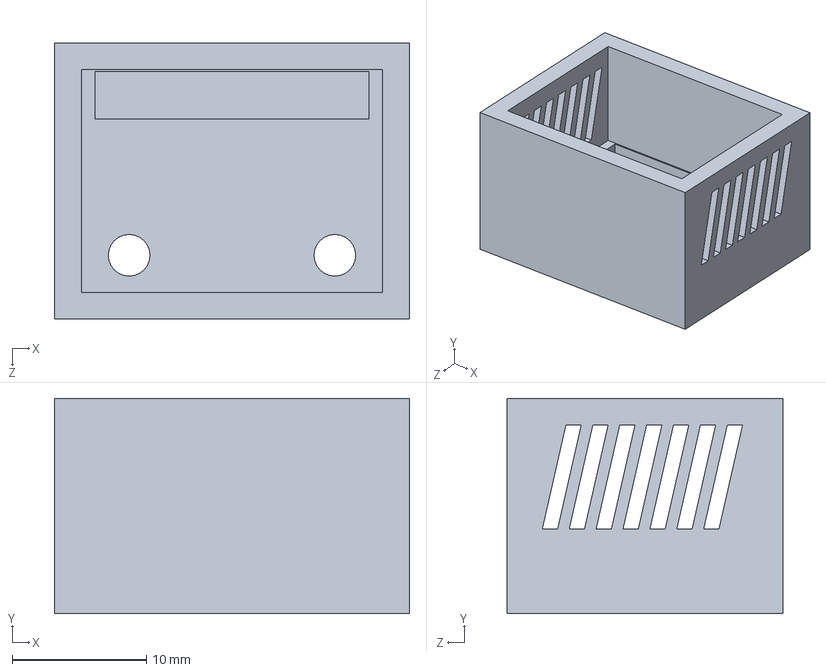
[picture p104: CAD file, 2025-08-24]
models/Prototypes/V6.5/IMU case.SLDPRT
26.4 x 16.0 x 20.5 mm
